doragasu/Balsamo/src/Balsamo/rtc.c

/************************************************************************//**
 * \file rtc.c
 * \brief Real Time Clock module
 *
 * \author Jesus Alonso Fernandez (doragasu)
 * \license GPL-3.0+ <http://www.gnu.org/licenses/gpl.html>
 *****************************************************************************/
/* This file is part of BALSAMO source package.
 *
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
 * You should have received a copy of the GNU General Public License
 * along with BALSAMO.  If not, see <http://www.gnu.org/licenses/>.
 */

#include <p30F6014.h>
#include "rtc.h"
#include "common.h"
#include "system.h"

/************************************************************************//**
 * \brief Enables low power 32768 Hz oscillator
 *
 * \note  Coded in assembly inside lposcen.s
 ****************************************************************************/
void LPOSCEnable(void);

/// Time keeping variables
static BYTE rtcYear = RTC_DEF_YEAR_NUM-1980, rtcMon = 1, rtcMday = 1,
	rtcHour = 0, rtcMin = 0, rtcSec = 0;

/// RTC interrupt handler. Called once each second to keep clock counting.
/// Generates RTC events each time minutes are incremented.
void __attribute__((interrupt, auto_psv)) _T1Interrupt (void)
{
	static const BYTE samurai[12] = {31, 28, 31, 30, 31, 30, 31, 31, 30, 31, 30, 31};
	BYTE maxDay;

	_T1IF = 0;			///< Clear T1 flag

    /// Update date and time
	if (++rtcSec >= 60)
	{
		rtcSec = 0;
		/// Generate a system event each minute
		SysIQueuePut(SYS_RTC_MINUTE);
		if (++rtcMin >= 60)
		{
			rtcMin = 0;
			if (++rtcHour >= 24)
			{
				rtcHour = 0;
				maxDay = samurai[rtcMon - 1];
				if ((maxDay == 28) && !(rtcYear & 3)) maxDay++;
				if (++rtcMday > maxDay)
				{
					rtcMday = 1;
					if (++rtcMon > 12)
					{
						rtcMon = 1;
						rtcYear++;
					}
				}
			}
		}
	}
}

/************************************************************************//**
 * \brief Starts the RTC.
 ****************************************************************************/
void RtcStart(void)
{
	/// Write OSCCONL unlock sequence, and enable LP Oscillator
	LPOSCEnable();
	PR1 = 32768 - 1;
	T1CON = 0x8002;
	/// Enable TIMER1 interrupt
	_T1IE = 1;
}

/************************************************************************//**
 * \brief Sets date and time (excepting year)
 *
 * \param[in] mon  Month to set (1 ~ 12).
 * \param[in] day  Day to set (1 ~ 31).
 * \param[in] hour Hour to set (0 ~ 23).
 * \param[in] min  Minute to set (0 ~ 59).
 * \param[in] sec  Second to set (0 ~ 59).
 ****************************************************************************/
void RtcSetTime(BYTE mon, BYTE day, BYTE hour, BYTE min, BYTE sec)
{
	_DI();

	rtcMon = mon;
	rtcMday = day;
	rtcHour = hour;
	rtcMin = min;
	rtcSec = sec;

	_EI();
}

/************************************************************************//**
 * \brief Sets year.
 *
 * \param[in] year Year to set (e.g. 2014).
 ****************************************************************************/
void RtcSetYear(WORD year)
{
	_DI();

	rtcYear = year - 1980;

	_EI();
}

/************************************************************************//**
 * \brief Gets time
 *
 * \param[out] hour Hour.
 * \param[out] min  Minute.
 * \param[out] sec  Second.
 ****************************************************************************/
void RtcGetTime(BYTE *hour, BYTE *min, BYTE *sec)
{
	_DI();

	*hour = rtcHour;
	*min = rtcMin;
	*sec = rtcSec;

	_EI();
}

/************************************************************************//**
 * \brief Gets date
 *
 * \param[out] year Year.
 * \param[out] mon  Month.
 * \param[out] day  Day.
 ****************************************************************************/
void RtcGetDate(WORD *year, BYTE *month, BYTE *day)
{
	_DI();

	*year = 1980 + rtcYear;
	*month = rtcMon;
	*day = rtcMday;

	_EI();
}

/************************************************************************//**
 * \brief Get timestamp formatted for fatfs
 *
 * \return Timestamp using fatfs format
 ****************************************************************************/
DWORD get_fattime(void)
{
	DWORD tmr;

	_DI();

	/* Pack date and time into a DWORD variable */
	tmr =	  (((DWORD)rtcYear - 80) << 25)
			| ((DWORD)rtcMon << 21)
			| ((DWORD)rtcMday << 16)
			| (WORD)(rtcHour << 11)
			| (WORD)(rtcMin << 5)
			| (WORD)(rtcSec >> 1);
	_EI();

	return tmr;
}
