doragasu/Balsamo/src/Balsamo/traps.c

/**********************************************************************
* © 2005 Microchip Technology Inc.
*
* FileName:        traps.c
* Dependencies:    p30fxxxx.h
* Processor:       dsPIC30F
* Compiler:        MPLAB® C30 v1.32.00 or higher
*
* SOFTWARE LICENSE AGREEMENT:
* Microchip Technology Inc. (“Microchip”) licenses this software to you
* solely for use with Microchip dsPIC® digital signal controller
* products. The software is owned by Microchip and is protected under
* applicable copyright laws.  All rights reserved.
*
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
* REVISION HISTORY:
*~~~~~~~~~~~~~~~~~~~~~~~~~~~~~~~~~~~~~~~~~~~~~~~~~~~~~~~~~~~~~~~~~~~~~~
* Author            Date      Comments on this revision
*~~~~~~~~~~~~~~~~~~~~~~~~~~~~~~~~~~~~~~~~~~~~~~~~~~~~~~~~~~~~~~~~~~~~~~
* Hrushikesh Vasuki 07/18/05  First release of source file
*
*~~~~~~~~~~~~~~~~~~~~~~~~~~~~~~~~~~~~~~~~~~~~~~~~~~~~~~~~~~~~~~~~~~~~~~
*
* ADDITIONAL NOTES:
* 1. This file contains trap service routines (handlers) for hardware
*    exceptions generated by the dsPIC30F device.
* 2. All trap service routines in this file simply ensure that device
*    continuously executes code within the trap service routine. Users
*    may modify the basic framework provided here to suit to the needs
*    of their application.
*
**********************************************************************/

#include "p30fxxxx.h"

void __attribute__((__interrupt__)) _OscillatorFail(void);
void __attribute__((__interrupt__)) _AddressError(void);
void __attribute__((__interrupt__)) _StackError(void);
void __attribute__((__interrupt__)) _MathError(void);
void __attribute__((__interrupt__)) _AltOscillatorFail(void);
void __attribute__((__interrupt__)) _AltAddressError(void);
void __attribute__((__interrupt__)) _AltStackError(void);
void __attribute__((__interrupt__)) _AltMathError(void);


/* Primary Exception Vector handlers:
   These routines are used if INTCON2bits.ALTIVT = 0.
   All trap service routines in this file simply ensure that device
   continuously executes code within the trap service routine. Users
   may modify the basic framework provided here to suit to the needs
   of their application. */

void __attribute__((__interrupt__)) _OscillatorFail(void)
{
        INTCON1bits.OSCFAIL = 0;        //Clear the trap flag
        while (1);
}

void __attribute__((__interrupt__)) _AddressError(void)
{
        INTCON1bits.ADDRERR = 0;        //Clear the trap flag
        while (1);
}

void __attribute__((__interrupt__)) _StackError(void)
{
        INTCON1bits.STKERR = 0;         //Clear the trap flag
        while (1);
}

void __attribute__((__interrupt__)) _MathError(void)
{
        INTCON1bits.MATHERR = 0;        //Clear the trap flag
        while (1);
}


/* Alternate Exception Vector handlers:
   These routines are used if INTCON2bits.ALTIVT = 1.
   All trap service routines in this file simply ensure that device
   continuously executes code within the trap service routine. Users
   may modify the basic framework provided here to suit to the needs
   of their application. */

void __attribute__((__interrupt__)) _AltOscillatorFail(void)
{
        INTCON1bits.OSCFAIL = 0;
        while (1);
}

void __attribute__((__interrupt__)) _AltAddressError(void)
{
        INTCON1bits.ADDRERR = 0;
        while (1);
}

void __attribute__((__interrupt__)) _AltStackError(void)
{
        INTCON1bits.STKERR = 0;
        while (1);
}

void __attribute__((__interrupt__)) _AltMathError(void)
{
        INTCON1bits.MATHERR = 0;
        while (1);
}
