doragasu/Balsamo/src/Balsamo/xlcd/PutsXLCD.c

#include "xlcd.h"
#include "delay.h"

#ifdef _RD10

/*******************************************************************
Function Name:          PutsXLCD
Description:            This function writes a string of characters 
                        into the LCD controller.it stops transmission
                        before the null character.(which is not sent).
Input parameters:       char  *buffer 
Return value:           void
********************************************************************/

void PutsXLCD(char *buffer)
{

    while(*buffer != '\0')
    {
        WriteDataXLCD(*buffer); /* calling another function */
                                /* to write each char to the lcd module */
        buffer++;
    }
} /* end of function */

#else
#warning "Does not build on this target"
#endif
